BoujeeEnjinia1701/wellsense/cad/drawings/WLS-DWG-001.pdf

CONCEPT, NOT FOR FABRICATION | WellSense · github.com/BoujeeEnjinia1701/wellsense

FRONT VIEW
Scale 1:25; looking at the front (along +Y)

TOP VIEW
Scale 1:25; looking down (along -Z)

RIGHT VIEW
Scale 1:25; looking at the right side (along -X)

1001

347 2906

GROUND

EXISTING WELL
(NOT IN BOM)

BOREHOLE CONTINUES
PROBE 30 m (DESIGN)

1750 FieldNode base

2100 post top

2,206 overall

600

583 cap
450 casing

750

6 JUNCTION BOX, 7 BOARD

5 CAP
AND GRIP

4 SEAL PLATE

8 FIELDNODE CORE (FND-BLD-001)

14 CONDUIT AND TAIL

16 SECURITY SCREW

200

16 PADLOCK ON EYE BOLT

16 HASP, PADLOCK

ISOMETRIC VIEW
Not to scale; seen from the front right and above, about 30 deg elevation

170

500 drilled

DETAIL A: PROBE ZONE
Scale 1:6; bottom of tube

1 PROBE

3 TUBE

MAIN DIMENSIONS AND INTERFACES (MM)
Casing 150 bore (existing), stick-up 450. Seal plate: split 200 x 20 HDPE, rim band Access tube 1 in Sch 40 PVC 33.4 x 26.6; 32 clear of riser
Probe 22 max x 170, 2.3 radial clearance; 30 m below casing top (to 60 m)
Post 48.3 x 3.2 galv., 2100 above ground, 600 in 300 footing
Junction box 90 x 120 x 160, center 1250, on a plate with V-blocks FieldNode core per FND-DWG-001; base 1750; sensor port A (I2C, 12 V rail)
Loop 4 to 20 mA from a 24 V boost; 150 ohm shunt (WLS-CAL-001)
Cable in 1/2 in galv. conduit (21.3 OD) and a flexible tail; locks per line 16
Third-angle; front view from -Y, FieldNode and panel face the equator; well on the Z axis
REV | DESCRIPTION | DATE | BY
P1 | Preliminary GA for TRL 3 (from cad/src/model.py) | 2026-09-25 | AC
P2 | 22 mm probe; conduit 14 added (WLS-DDR-002) | 2026-09-25 | AC
P3 | FieldNode panel tilt corrected to face -Y (WLS-DDR-003) | 2026-09-27 | AC
P4 | Layout and labels tidied | 2026-09-27 | AC
P5 | Constructable design (WLS-DDR-004) | 2026-10-02 | AC
P6 | Locks added, line 16 (WLS-DEC-001) | 2026-10-02 | AC
WELLSENSE | github.com/BoujeeEnjinia1701/wellsense

## General arrangement

DRAWING NO.
WLS-DWG-001

REV
P6

SHEET
1 of 1

SIZE

## ANSI B

SCALE
1:25

UNITS
mm
PROJECTION | DATE
2026-10-02

DRAWN
Amish Chadha

MATERIAL / NOTES
Bought-in parts per bom/bom.csv; borehole not drawn below -700. PRELIMINARY, NOT FOR FABRICATION
Licensed CERN-OHL-S-2.0 · Design Molecule Lab · designmolecule.com | Generated from cad/src; do not edit by hand
