BoujeeEnjinia1701/wellsense/cad/drawings/WLS-DWG-109.pdf

### BUILD PLAN SKETCH, PLAN NOT YET BUILT WellSense · github.com/BoujeeEnjinia1701/wellsense

FRONT VIEW
Scale 1:1; looking at the front (along +Y)

TOP VIEW
Scale 1:1; looking down (along -Z)

RIGHT VIEW
Scale 1:1; looking at the right side (along -X)

42

65 45

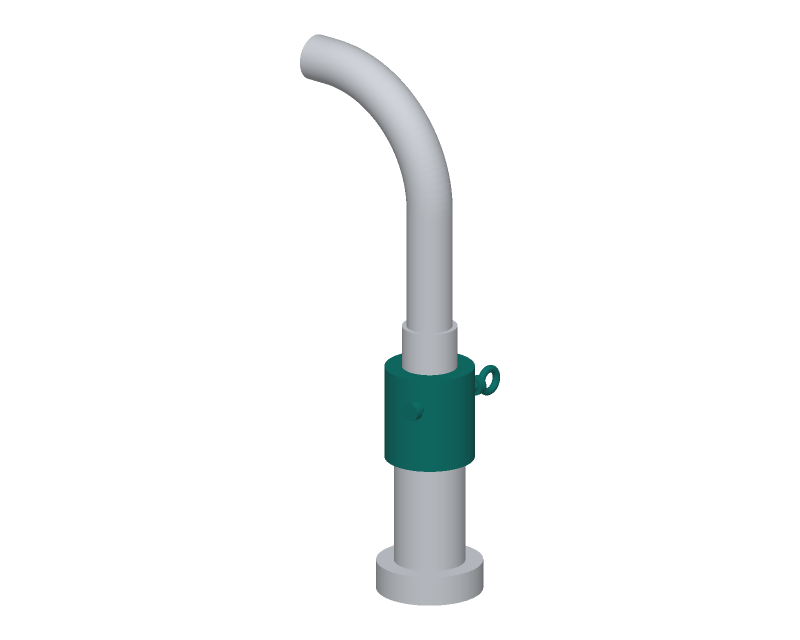
[picture p7: figure]

WHERE IT GOES
This part in colour, its neighbours in grey

HOW TO MAKE IT AND HOW IT FITS
Do not glue the cap: it lifts off with the probe for calibration.
Top: drill 22.5 mm in the centre for the 1/2 in conduit connector. Side: drill 5 mm straight across, 9 above the tube end (the cap's shoulder) and 9 off the centre line, for the M5 eye bolt (the cross bolt). The bolt passes beside the cable, never through it.
Fit: the conduit connector goes through the top with its locknut
inside. The cable support grip's eye goes over the cross bolt,
which then carries the probe and cable; nyloc nut on the -Y side. The eye on the +Y side takes the padlock (WLS-DEC-001).
The cap sits on the tube end by its own weight and the load.
Check: with the bolt in, the cap still slides on and off the tube.
REV | DESCRIPTION | DATE | BY
P1 | Making sketch for the prototype build plan | 2026-10-02 | AC
P2 | Cross bolt is an eye bolt for the padlock (WLS-DEC-001) | 2026-10-02 | AC
WELLSENSE | github.com/BoujeeEnjinia1701/wellsense

## WellSense tube cap: making sketch

DRAWING NO.
WLS-DWG-109

REV
P2

SHEET
1 of 1

SIZE

## ANSI B

SCALE
1:1

UNITS
mm
PROJECTION | DATE
2026-10-02

DRAWN
Amish Chadha

MATERIAL / NOTES
1 in Sch 40 PVC slip cap; stainless M5 x 50 eye bolt
Licensed CERN-OHL-S-2.0 · Design Molecule Lab · designmolecule.com | Generated from cad/src; do not edit by hand
