BoujeeEnjinia1701/wellsense/cad/drawings/WLS-DWG-101.pdf

### BUILD PLAN SKETCH, PLAN NOT YET BUILT WellSense · github.com/BoujeeEnjinia1701/wellsense

FRONT VIEW
Scale 1:25; looking at the front (along +Y)

TOP VIEW
Scale 1:25; looking down (along -Z)

RIGHT VIEW
Scale 1:25; looking at the right side (along -X)

51

51 2708

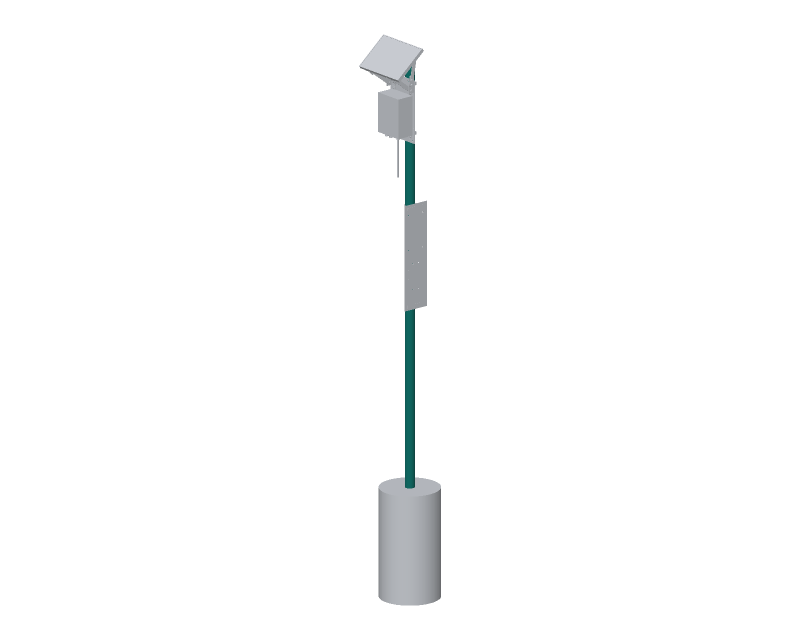
[picture p49: figure]

WHERE IT GOES
This part in colour, its neighbours in grey

HOW TO MAKE IT AND HOW IT FITS
Cut the pipe to 2,700 mm, square; file the ends; paint each cut end with zinc-rich paint so the galvanizing is made good.
Push the plastic cap into the top end.
Mark with tape, measured up from the bottom end: 600 (ground level), 1,480 and 1,970 (junction box bands), 2,330 and 2,580 (FieldNode bands). These are guides only; the parts are set by eye on site.
No holes are drilled in the post: everything clamps to it.
Fit: 600 mm stands in a 300 mm concrete footing, 2,100 mm above ground, plumb in both directions, 750 mm from the well centre. Check: straight within 5 mm over its length; the cap is a push fit.
REV | DESCRIPTION | DATE | BY
P1 | Making sketch for the prototype build plan | 2026-10-02 | AC
WELLSENSE | github.com/BoujeeEnjinia1701/wellsense

## WellSense post: making sketch

DRAWING NO.
WLS-DWG-101

REV
P1

SHEET
1 of 1

SIZE

## ANSI B

SCALE
1:25

UNITS
mm
PROJECTION | DATE
2026-10-02

DRAWN
Amish Chadha

MATERIAL / NOTES
Galvanized steel pipe 48.3 x 3.2 mm (1-1/2 in), 2.7 m
Licensed CERN-OHL-S-2.0 · Design Molecule Lab · designmolecule.com | Generated from cad/src; do not edit by hand
