BoujeeEnjinia1701/wellsense/cad/drawings/WLS-DWG-102.pdf

### BUILD PLAN SKETCH, PLAN NOT YET BUILT WellSense · github.com/BoujeeEnjinia1701/wellsense

FRONT VIEW
Scale 1:5; looking at the front (along +Y)

TOP VIEW
Scale 1:5; looking down (along -Z)

RIGHT VIEW
Scale 1:5; looking at the right side (along -X)

140

3 530

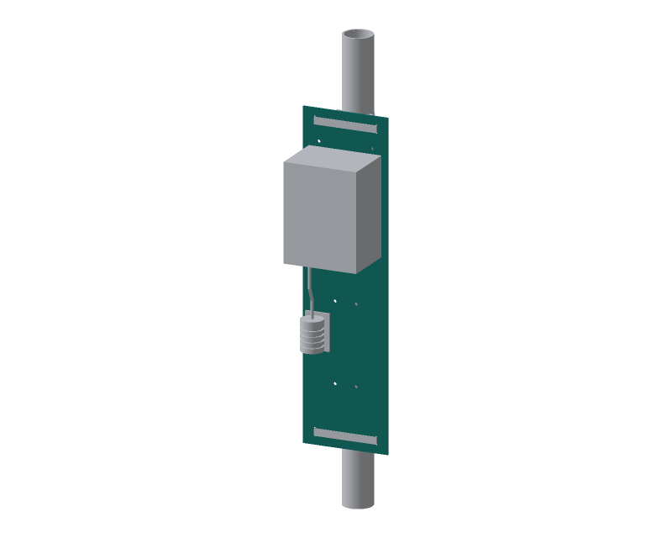
[picture p50: figure]

WHERE IT GOES
This part in colour, its neighbours in grey

HOW TO MAKE IT AND HOW IT FITS
Blank 140 x 530 mm. Front view is the face the box sits on. Heights up from the bottom edge; sideways from the centre line. Band slots 3 x 15 at 51 each side, centred 20 and 510 up:
chain drill 3 mm and file square. The bands go through these. V-block screws 4.5, countersunk from the front, at 18 each side, 20 and 510 up.
Lug screws 5.5 at 44 each side, 302 and 478 up.
Saddle screws 5.5 at 17.4 each side, 100 and 230 up. Barometric housing 4.5 at 45 to the left (seen from the front), 158 and 202 up.
Deburr every hole and edge; round the corners about 2 mm. Check: lay the V-blocks, lugs and saddles on it and look through each hole; the holes must line up without forcing a screw.
REV | DESCRIPTION | DATE | BY
P1 | Making sketch for the prototype build plan | 2026-10-02 | AC
WELLSENSE | github.com/BoujeeEnjinia1701/wellsense

## WellSense junction box plate: making sketch

DRAWING NO.
WLS-DWG-102

REV
P1

SHEET
1 of 1

SIZE

## ANSI B

SCALE
1:5

UNITS
mm
PROJECTION | DATE
2026-10-02

DRAWN
Amish Chadha

MATERIAL / NOTES
Aluminium sheet 3 mm, 5052 or 6061 class
Licensed CERN-OHL-S-2.0 · Design Molecule Lab · designmolecule.com | Generated from cad/src; do not edit by hand
