BoujeeEnjinia1701/wellsense/cad/drawings/WLS-DWG-103.pdf

### BUILD PLAN SKETCH, PLAN NOT YET BUILT WellSense · github.com/BoujeeEnjinia1701/wellsense

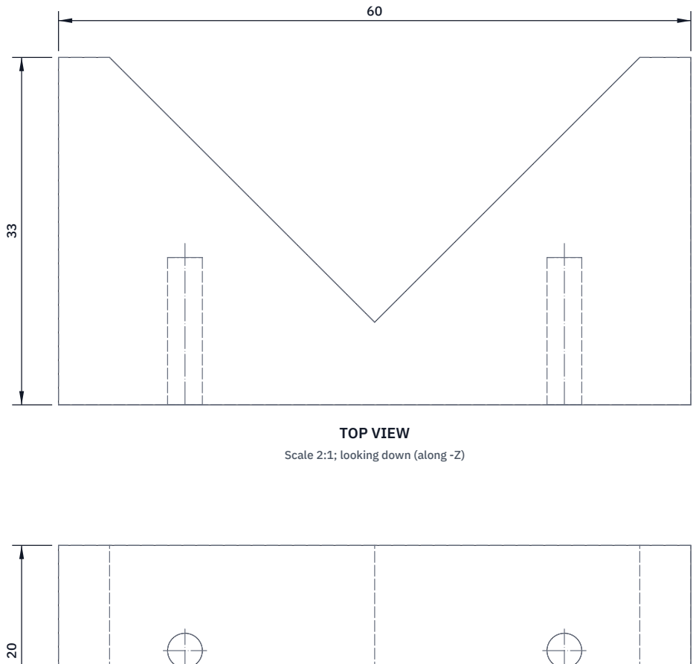
[picture p51: figure]
TOP VIEW; Scale 2:1; looking down (along -Z)
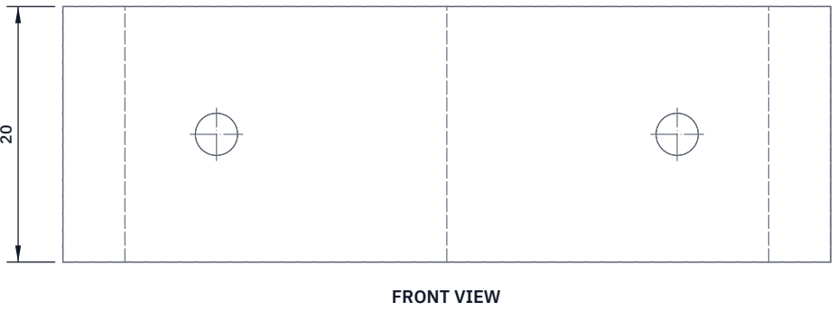
[picture p52: figure]
FRONT VIEW

Scale 2:1; looking at the front (along +Y)

RIGHT VIEW
Scale 2:1; looking at the right side (along -X)

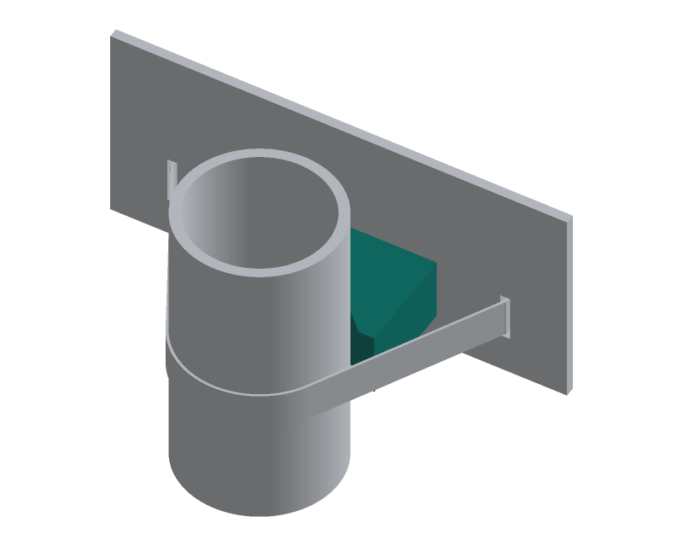
[picture p53: figure]

WHERE IT GOES
This part in colour, its neighbours in grey

HOW TO MAKE IT AND HOW IT FITS
Make two, the same as FieldNode's V-blocks. Saw a 20 mm slice off 60 x 40 bar; saw and file it to 60 wide x 33 deep x 20 tall.
The flat back goes on the junction box plate.
Scribe a 90 degree V on both 60 x 33 faces with a 45 degree square: 50.3 wide at the front face, point 7.8 from the back face.
Saw just inside both lines, file to the lines, keep the faces flat. Break the V's front edges 0.5 mm so they cannot scratch the post. Drill 3.3, 14 deep, and tap M4 12 deep in the back face, 18 each side of centre, half way up (10).
Fit: two M4 countersunk screws from the front of the plate.
The 48.3 post touches both V faces; it never touches the bottom. Check: on the post the block must not rock; light shows at the bottom of the V, not along its faces.
REV | DESCRIPTION | DATE | BY
P1 | Making sketch for the prototype build plan | 2026-10-02 | AC
WELLSENSE | github.com/BoujeeEnjinia1701/wellsense

## WellSense V-block (make 2): making sketch

DRAWING NO.
WLS-DWG-103

REV
P1

SHEET
1 of 1

SIZE

## ANSI B

SCALE
2:1

UNITS
mm
PROJECTION | DATE
2026-10-02

DRAWN
Amish Chadha

MATERIAL / NOTES
Aluminium flat bar 60 x 40 mm, 6082 or 6061
Licensed CERN-OHL-S-2.0 · Design Molecule Lab · designmolecule.com | Generated from cad/src; do not edit by hand
