BoujeeEnjinia1701/wellsense/cad/drawings/WLS-DWG-104.pdf

### BUILD PLAN SKETCH, PLAN NOT YET BUILT WellSense · github.com/BoujeeEnjinia1701/wellsense

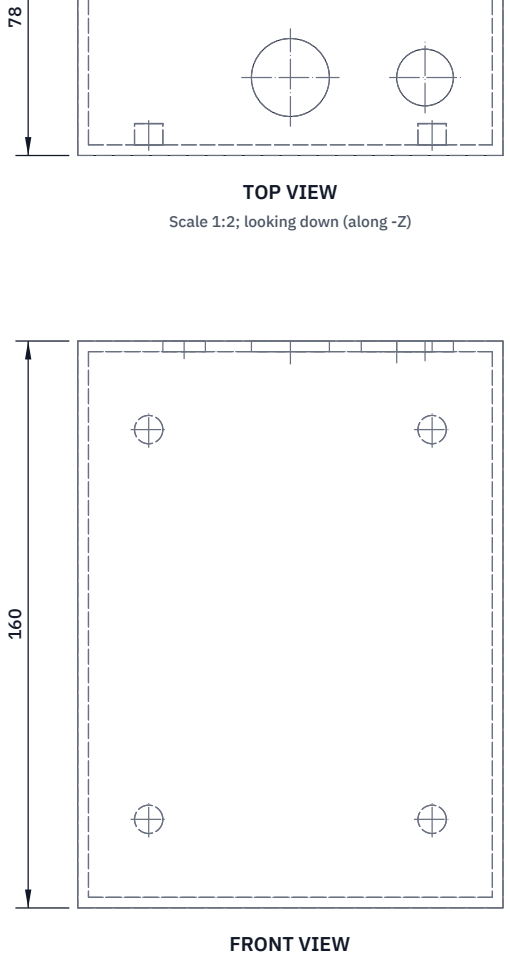
[picture p54: figure]
FRONT VIEW; TOP VIEW; Scale 1:2; looking down (along -Z)

Scale 1:2; looking at the front (along +Y)

RIGHT VIEW
Scale 1:2; looking at the right side (along -X)

120

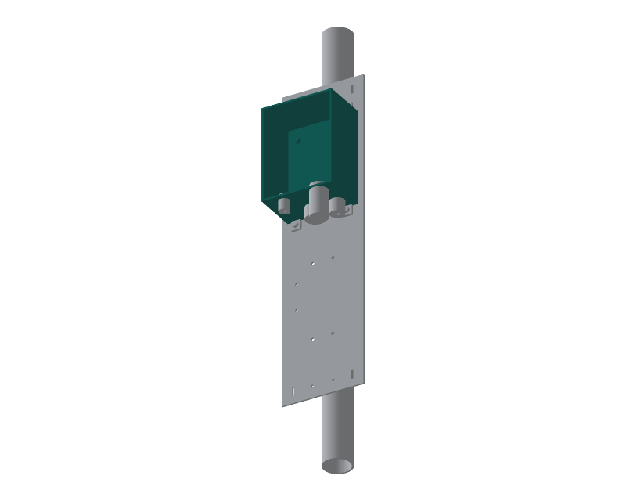
[picture p55: figure]

WHERE IT GOES
This part in colour, its neighbours in grey

HOW TO MAKE IT AND HOW IT FITS
Drawn upside down: stand the box on its top, back face toward you; the top view then shows the bottom face as it lies on the bench. Measure forward from the back face and sideways from the centre line (left and right as seen from the front, the lid side).
Back row, 22 from the back face: conduit hub 22 hole on the centre line; M16 gland 16 hole at 38 right.
Front row, 62 from the back face: breather 20 hole at 30 right;
M12 gland 12 hole at 30 left.
Tape the face, pilot drill 3 slowly with wood behind, open out with a step drill. No solvents: polycarbonate crazes. Deburr.
Check each size against the part's datasheet before the last step. Fit the four lugs to the back corners as the lug kit's maker says. Check: no crack runs out of any hole under a bright lamp.
REV | DESCRIPTION | DATE | BY
P1 | Making sketch for the prototype build plan | 2026-10-02 | AC
WELLSENSE | github.com/BoujeeEnjinia1701/wellsense

## WellSense junction box body: drilling sketch

DRAWING NO.
WLS-DWG-104

REV
P1

SHEET
1 of 1

SIZE

## ANSI B

SCALE
1:2

UNITS
mm
PROJECTION | DATE
2026-10-02

DRAWN
Amish Chadha

MATERIAL / NOTES
Bought IP66 polycarbonate box 160 x 120 x 90 mm with bosses and lug kit
Licensed CERN-OHL-S-2.0 · Design Molecule Lab · designmolecule.com | Generated from cad/src; do not edit by hand
