BoujeeEnjinia1701/wellsense/cad/drawings/WLS-DWG-105.pdf

### BUILD PLAN SKETCH, PLAN NOT YET BUILT WellSense · github.com/BoujeeEnjinia1701/wellsense

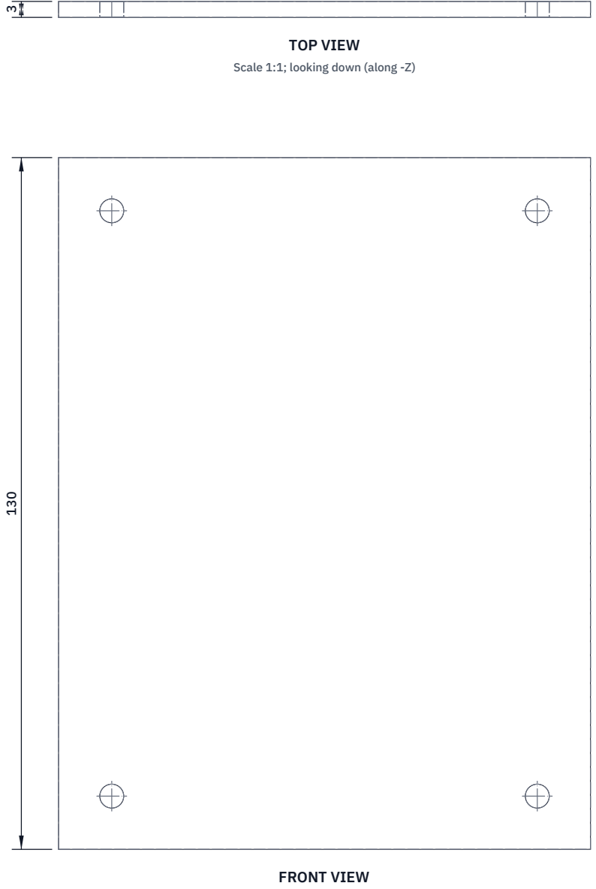
[picture p56: figure]
FRONT VIEW; TOP VIEW; Scale 1:1; looking down (along -Z)

Scale 1:1; looking at the front (along +Y)

RIGHT VIEW
Scale 1:1; looking at the right side (along -X)

100

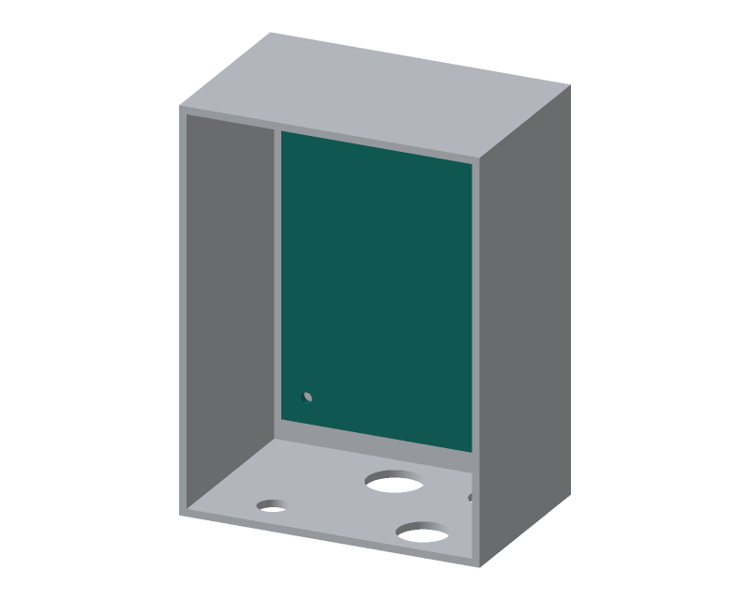
[picture p57: figure]

WHERE IT GOES
This part in colour, its neighbours in grey

HOW TO MAKE IT AND HOW IT FITS
Print flat, 100 x 130 x 3 mm, in ASA in an enclosed printer.
Four 4.5 holes, 80 apart across and 110 apart up and down, 10 in from the top and bottom edges: they meet the box's four moulded bosses. Measure your box's bosses first and move the holes to suit. Lay out on the front: boost module upper left, ADC and shunt upper right, regulator and surge board below it, terminal strip along
the bottom (left and right as seen from the lid side).
Mark each module's holes through the module; drill 3.2 for M3 screws on 6 mm nylon standoffs.
Fit: four M4 screws into the bosses; the plate stands 6 mm off the back wall and 12 mm above the floor, clear of the entry nuts. Check: flat within 0.5 mm; drops in and lifts out without force.
REV | DESCRIPTION | DATE | BY
P1 | Making sketch for the prototype build plan | 2026-10-02 | AC
WELLSENSE | github.com/BoujeeEnjinia1701/wellsense

## WellSense internal plate: making sketch

DRAWING NO.
WLS-DWG-105

REV
P1

SHEET
1 of 1

SIZE

## ANSI B

SCALE
1:1

UNITS
mm
PROJECTION | DATE
2026-10-02

DRAWN
Amish Chadha

MATERIAL / NOTES
ASA, 3D printed, 100 % infill
Licensed CERN-OHL-S-2.0 · Design Molecule Lab · designmolecule.com | Generated from cad/src; do not edit by hand
