BoujeeEnjinia1701/wellsense/cad/drawings/WLS-DWG-106.pdf

### BUILD PLAN SKETCH, PLAN NOT YET BUILT WellSense · github.com/BoujeeEnjinia1701/wellsense

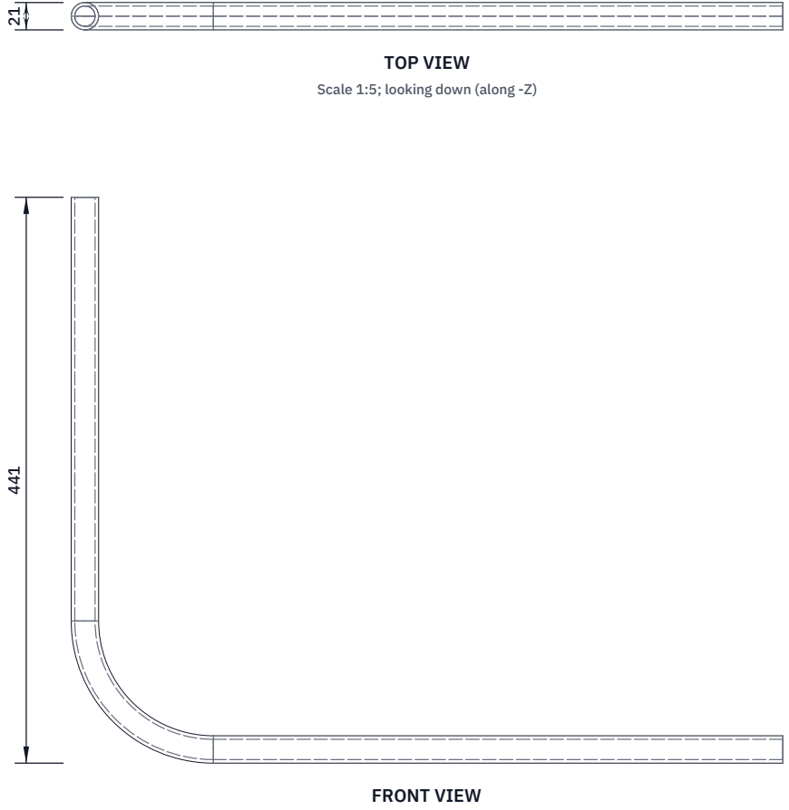
[picture p58: figure]
FRONT VIEW; TOP VIEW; Scale 1:5; looking down (along -Z)

Scale 1:5; looking at the front (along +Y)

RIGHT VIEW
Scale 1:5; looking at the right side (along -X)

554

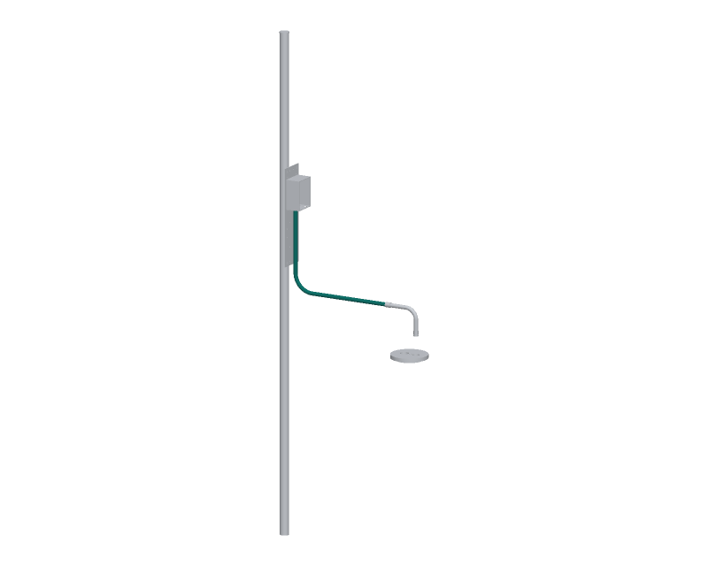
[picture p59: figure]

WHERE IT GOES
This part in colour, its neighbours in grey

HOW TO MAKE IT AND HOW IT FITS
One length with one 90 degree bend, 100 mm centre-line radius, made with a 1/2 in hand conduit bender.
Long leg (horizontal, toward the well): 543 to the bend's corner; short leg (vertical, into the box): 430
to the corner. Developed length about 0.95 m.
Mark the bend from the corner back along each leg; bend, then check the angle with a square and trim the ends to length.
Cut with a hacksaw or tube cutter, ream the ends so the bore cannot cut the cable, and paint each cut end with zinc-rich paint. Fit: the short end screws into the hub under the box; two spacer saddles hold it to the plate; the long end takes the connector
of the flexible tail over the well.
Check: both legs square; the ends are smooth inside.
REV | DESCRIPTION | DATE | BY
P1 | Making sketch for the prototype build plan | 2026-10-02 | AC
WELLSENSE | github.com/BoujeeEnjinia1701/wellsense

## WellSense rigid conduit: making sketch

DRAWING NO.
WLS-DWG-106

REV
P1

SHEET
1 of 1

SIZE

## ANSI B

SCALE
1:5

UNITS
mm
PROJECTION | DATE
2026-10-02

DRAWN
Amish Chadha

MATERIAL / NOTES
1/2 in galvanized rigid conduit, 21.3 mm OD
Licensed CERN-OHL-S-2.0 · Design Molecule Lab · designmolecule.com | Generated from cad/src; do not edit by hand
