BoujeeEnjinia1701/wellsense/cad/drawings/WLS-DWG-107.pdf

### BUILD PLAN SKETCH, PLAN NOT YET BUILT WellSense · github.com/BoujeeEnjinia1701/wellsense

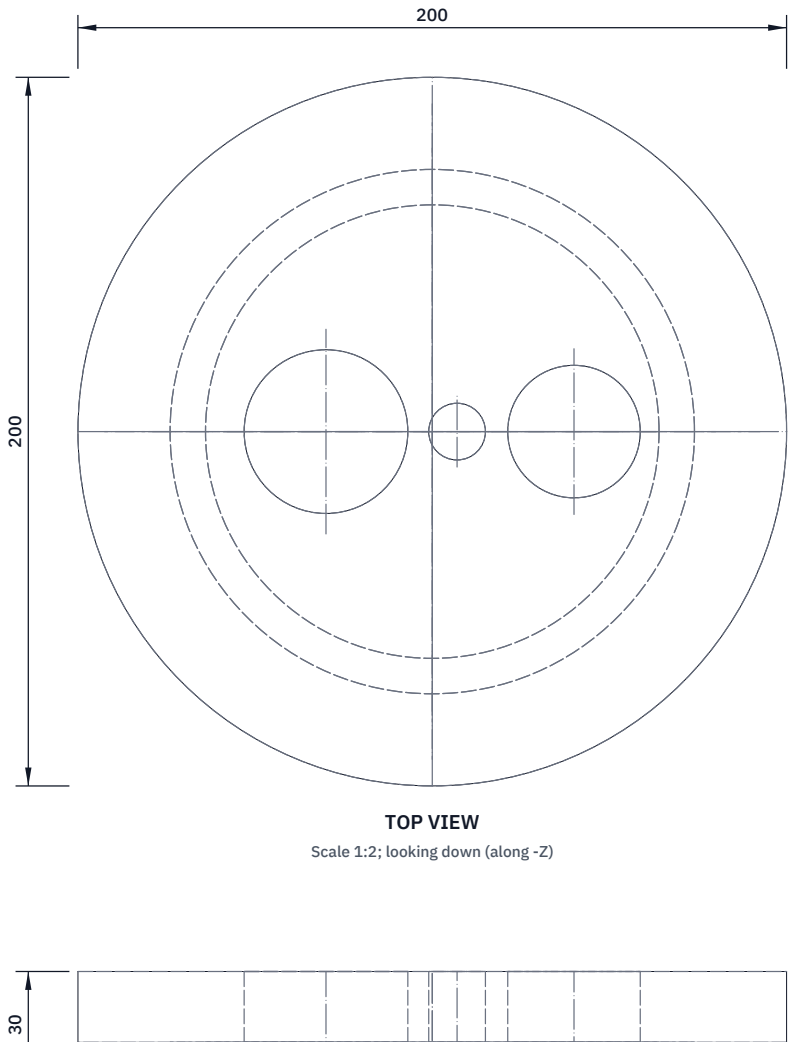
[picture p60: figure]
TOP VIEW; Scale 1:2; looking down (along -Z)

FRONT VIEW
Scale 1:2; looking at the front (along +Y)

RIGHT VIEW
Scale 1:2; looking at the right side (along -X)

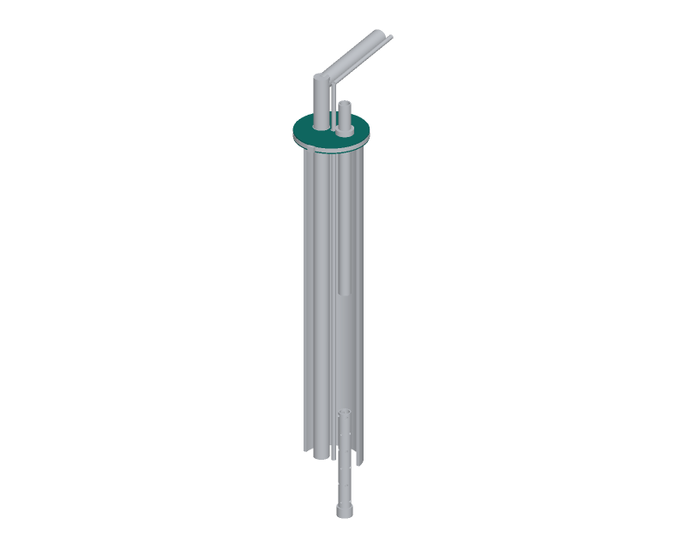
[picture p61: figure]

WHERE IT GOES
This part in colour, its neighbours in grey

HOW TO MAKE IT AND HOW IT FITS
Plate: a 200 mm disc of 20 mm HDPE. Spigot: a ring of 10 mm HDPE, 148 outside, 128 inside. Cut both with a jigsaw and a circle jig;
file to the line. Check the spigot slides into your casing.
Holes on one diameter: riser 46 at 30 left of centre,
pump cable 16 at 7 right, tube 37.4 at 40 right.
Change them to suit your well: measure the riser and cable first. Saw the disc and the ring in half along that diameter.
Screw each half ring under its plate half with three stainless
4 x 16 screws, pilot drilled 3 mm.
Gasket: 3 mm EPDM, 184 outside, 150 inside, cut once to fit. Wraps: 2 mm EPDM strips, 20 wide, one turn round the riser, the pump cable and the tube.
Fit: the halves meet round the wraps; a band clamp round the rim pulls them together. Check: halves meet with no daylight.
REV | DESCRIPTION | DATE | BY
P1 | Making sketch for the prototype build plan | 2026-10-02 | AC
WELLSENSE | github.com/BoujeeEnjinia1701/wellsense

## WellSense split seal plate with spigot rings: making sketch

DRAWING NO.
WLS-DWG-107

REV
P1

SHEET
1 of 1

SIZE

## ANSI B

SCALE
1:2

UNITS
mm
PROJECTION | DATE
2026-10-02

DRAWN
Amish Chadha

MATERIAL / NOTES
HDPE sheet 20 mm and 10 mm, drinking-water grade; EPDM 3 mm and 2 mm
Licensed CERN-OHL-S-2.0 · Design Molecule Lab · designmolecule.com | Generated from cad/src; do not edit by hand
