BoujeeEnjinia1701/wellsense/cad/drawings/WLS-DWG-108.pdf

### BUILD PLAN SKETCH, PLAN NOT YET BUILT WellSense · github.com/BoujeeEnjinia1701/wellsense

FRONT VIEW
Scale 1:5; looking at the front (along +Y)

TOP VIEW
Scale 1:5; looking down (along -Z)

RIGHT VIEW
Scale 1:5; looking at the right side (along -X)

42

42 615

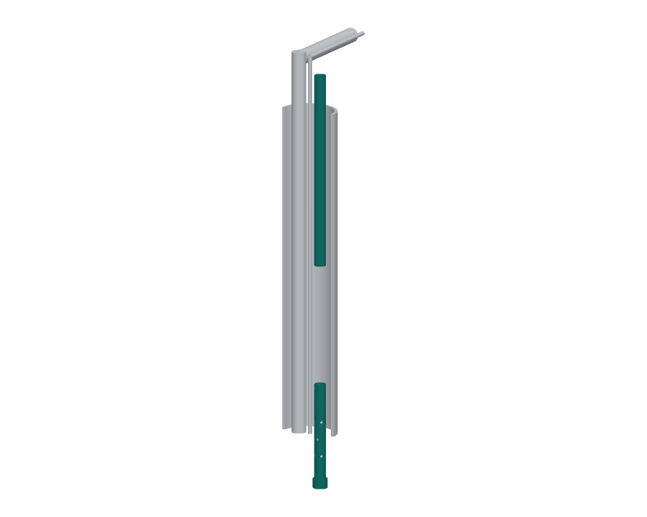
[picture p62: figure]

WHERE IT GOES
This part in colour, its neighbours in grey

HOW TO MAKE IT AND HOW IT FITS
Length: probe depth plus 0.5 m below it and 0.11 m above the casing top; in 3 m lengths joined with solvent-weld couplings. Joints
must be smooth inside so the probe cannot catch.
Bottom 0.5 m: 10 rings of 8 mm holes, rings 50 apart, the first
40 up from the end. Each ring is two holes drilled straight through at right angles (four holes); turn the next ring 45 degrees.
Drill in a V-block; deburr inside with a round file.
Solvent-weld the slip cap on the bottom end; drill one 8 mm drain hole in the cap so water can leave when the tube is lifted. Top end: cut square 110 mm above the casing top; deburr. The probe hangs 50 mm above the end, inside the drilled zone. Check: a 22 mm rod drops through the whole tube freely.
REV | DESCRIPTION | DATE | BY
P1 | Making sketch for the prototype build plan | 2026-10-02 | AC
WELLSENSE | github.com/BoujeeEnjinia1701/wellsense

## WellSense access tube, drilled end: making sketch

DRAWING NO.
WLS-DWG-108

REV
P1

SHEET
1 of 1

SIZE

## ANSI B

SCALE
1:5

UNITS
mm
PROJECTION | DATE
2026-10-02

DRAWN
Amish Chadha

MATERIAL / NOTES
1 in Sch 40 PVC pressure pipe 33.4 x 26.6 mm and a 1 in slip cap
Licensed CERN-OHL-S-2.0 · Design Molecule Lab · designmolecule.com | Generated from cad/src; do not edit by hand
