BoujeeEnjinia1701/wellsense/cad/drawings/WLS-DWG-001.png

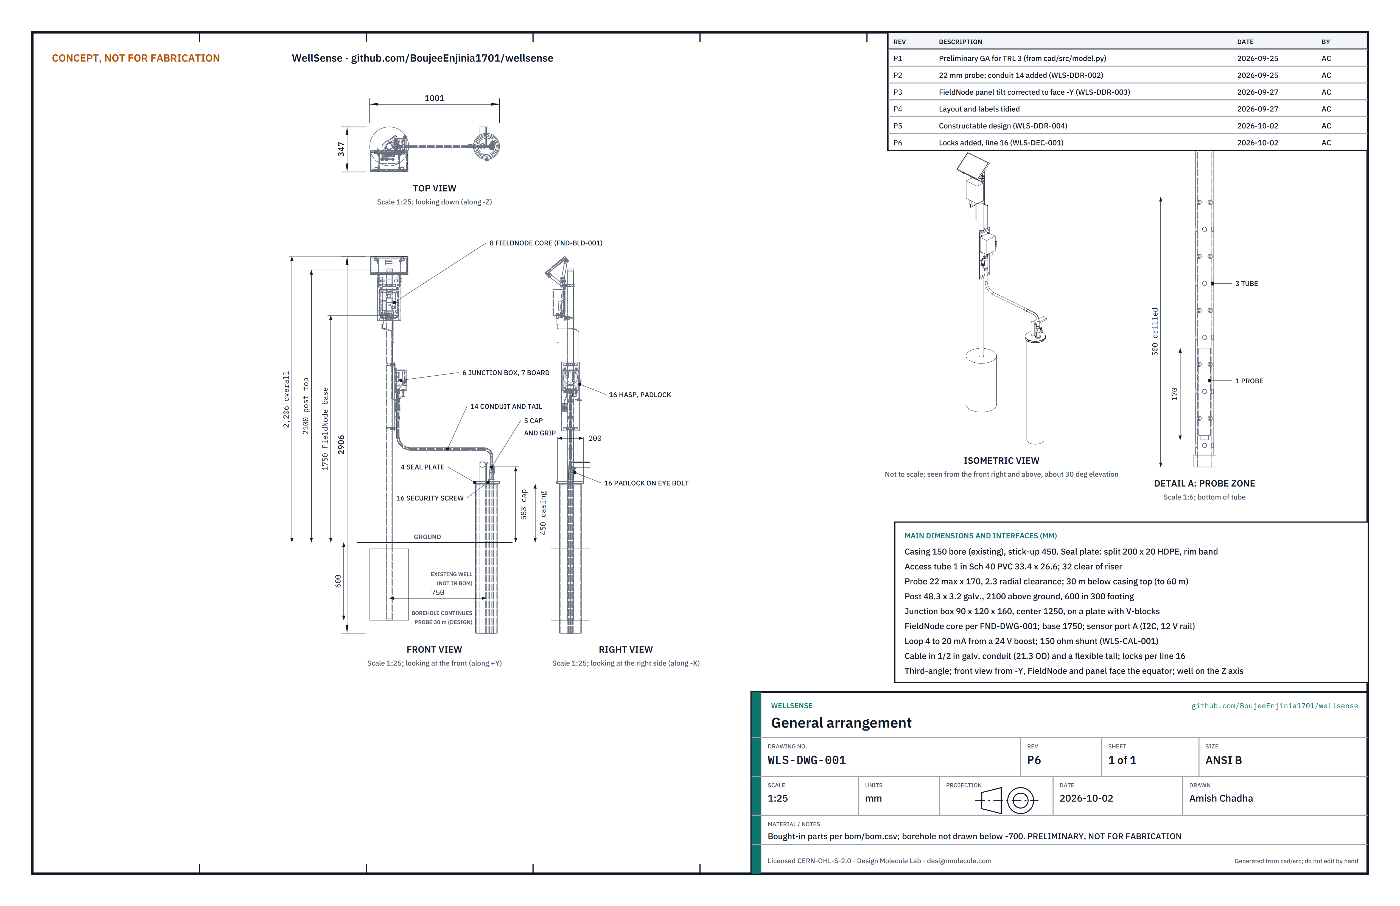
cad/drawings/WLS-DWG-001.png
