BoujeeEnjinia1701/wellsense/media/card.png

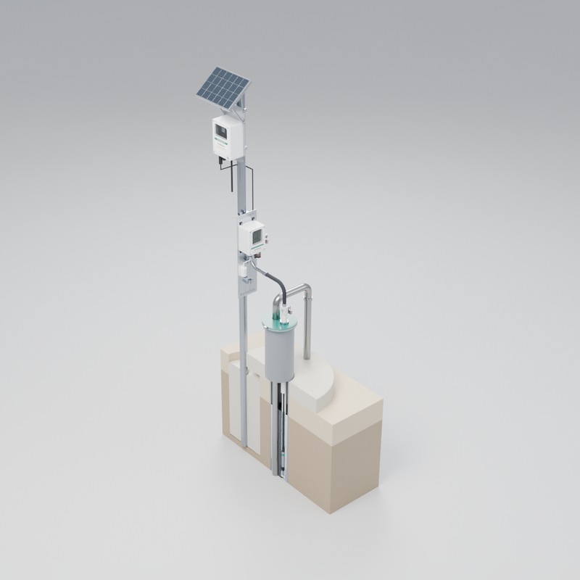
media/card.png
