BoujeeEnjinia1701/wellsense/media/concept-blueprint.png

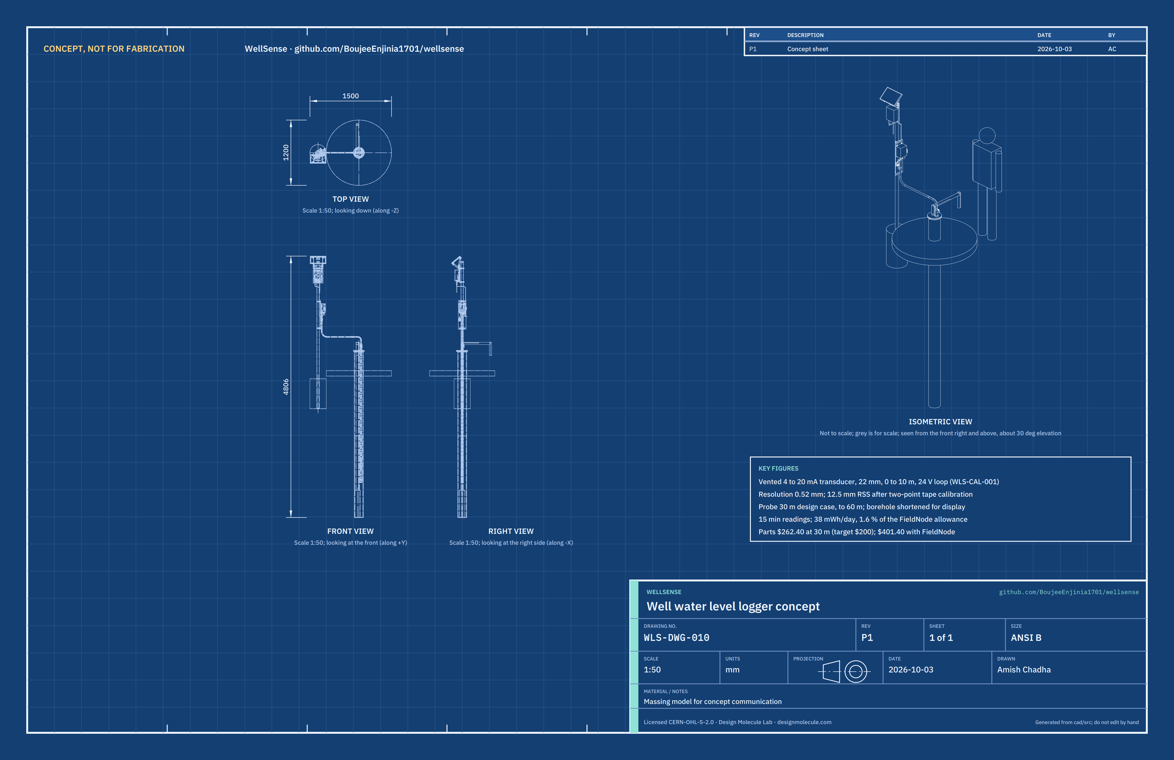
media/concept-blueprint.png
