BoujeeEnjinia1701/wellsense/media/render-detail.png

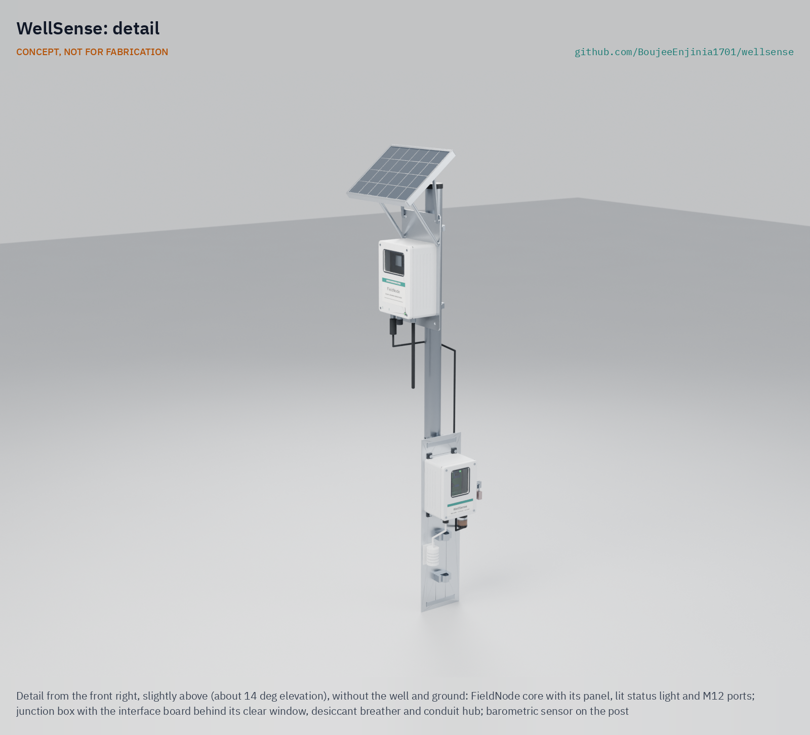
media/render-detail.png
