BoujeeEnjinia1701/wellsense/media/render-exploded.png

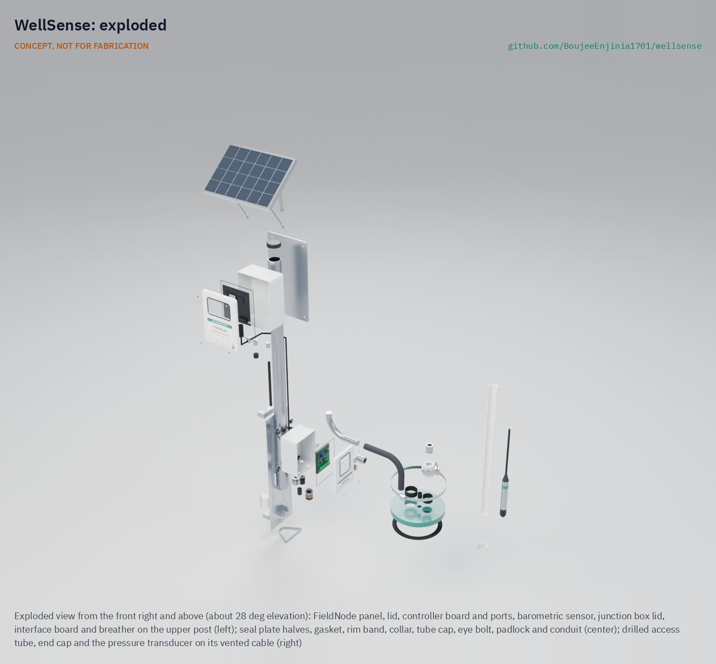
media/render-exploded.png
