BoujeeEnjinia1701/wellsense/media/social-preview.png

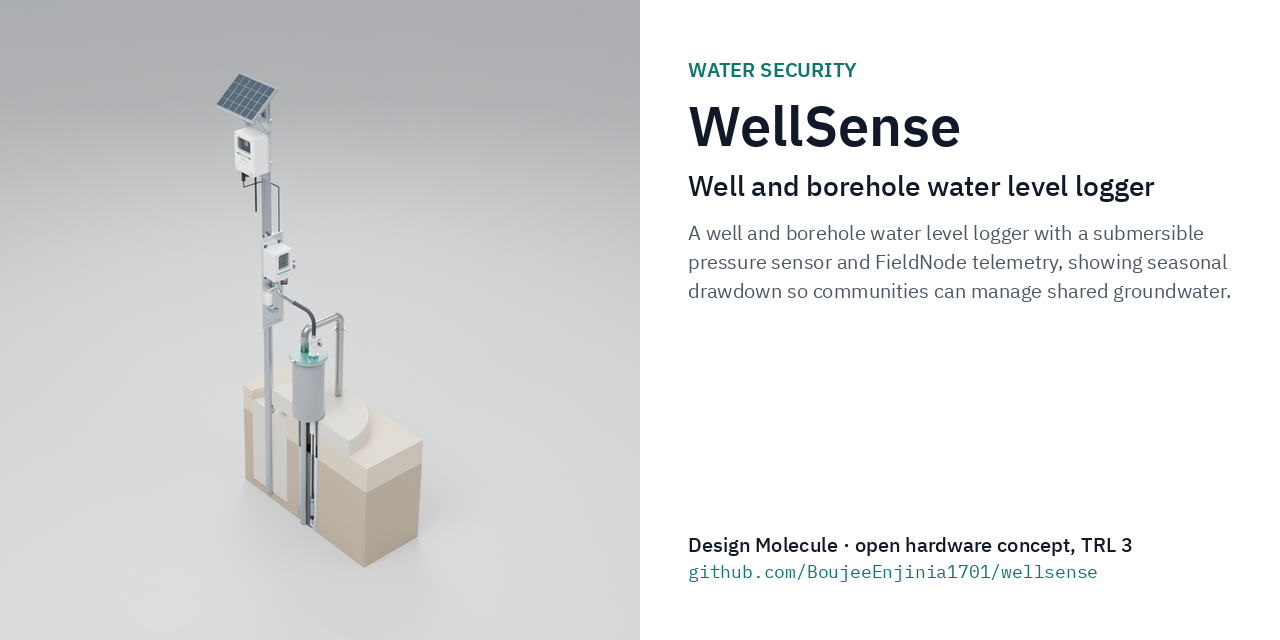
media/social-preview.png
